twinone/rubik-robot/scad/gripper/buildvars.scad

function cube_size() = 56;
function tolerance() = 0.2;
function screw_r() = 3/2;
function arm_width() = 7;
function arm_length() = 35;
function servo_base_height() = 4;
function servo_elevation() = 5;
function gear_r() = 11;
function arm_c2c() = gear_r()*2.35;

function arm_inset_x() = arm_width() + 2;
function arm_inset_y() = gear_r()+arm_width();
