twinone/rubik-robot/scad/gripper/util.scad

use <buildvars.scad>

module screw_hole() {
	circle(r=screw_r()+tolerance());
}
