twinone/rubik-robot/scad/util/util.scad

use <../buildvars.scad>

module screw_hole() {
	circle(r=screw_r()+tolerance());
}
